prydin/classab-amp-mosfet/spice/class_ab.asc

C1: cap; 33µ
C2: cap; 68p
C3: cap; 100n
C4: cap; 220µ
C5: cap; 220p
C6: cap; 47µ
C7: cap; 159.2n
C8: cap; 79.62n
C9: cap; 79.62n
C10: cap; 7m
C12: cap; 7m
C105: cap; 240µ
C111: cap; 12µ
D2: diode; 1N4148
D4: zener; UMZ5_1N
D5: zener; UMZ5_1N
D7: diode; RFUH5TF6S
D8: diode; RFUH5TF6S
D9: diode; 1N4148
L1: ind; 10µ
L3: ind; 1m
L102: ind; 0.43m
L103: ind; 127m
M1: nmos; IRFP240
M2: pmos; IRFP9240
Q1: npn; 2N5550
Q2: npn; 2N5550
Q3: pnp; 2N5401
Q4: pnp; 2N5401
Q6: pnp; BD140C
Q7: npn; BD139C
Q8: npn; BD139C
Q11: npn; 2N5550
Q12: npn; 2N5550
Q15: npn; 2N5550
Q16: pnp; 2N5401
R1: res; 150
R2: res; 22k
R3: res; 470
R4: res; 470
R5: res; 470
R6: res; 4.7k
R7: res; 1k
R8: res; 330
R9: res; 22k
R10: res; 100
R11: res; 4.7k
R12: res; 410
R13: res; 10k
R14: res; 100
R15: res; 100
R16: res; 0.33
R17: res; 0.33
R18: res; 2k
R19: res; 1k
R20: res; 10
R21: res; 10
R22: res; 100
R23: res; 2k
R28: res; 1k
R31: res; 8
R32: res; 330
R114: res; 6
R122: res; 137
V1: voltage; 40
V2: voltage; PULSE(-1.2 1.2 0.5m 1n 1n 0.5m 1m); AC 0
V3: voltage; 40
V4: voltage; ""; AC 1
V5: voltage; SINE(0 0.3 1k)
Named nets: 0, IN, B-, B+, OUT, NEG_IN, FB
.tran 0 200m 0 500n
.four 1k 50 -1 v(out)
.option plotwinsize 0
.ac dec 1000 1 10000k
SPEAKER MODEL
-4.5V
0V
.param Freq=1k
.options plotwinsize=0 numdgt=15 NoOpiter
Simulation Parameters
.option NoMarch
.tran 0 {stop} {start} {maxstep}
.param numsamples=32
.options gminsteps=0 srcsteps=500
.param period {1/f1}
.param stop {start+sampletime}
It's often (meaning almost always) desirable to delay capturing samples for the FFT to let 
the DC conditions in the circuit stabilize.  Larger capacitors in the circuit require higher 
values of delay.  But, they charge up based on time, not cycles of the test frequency.
So, this delay is in *seconds.*
.param SettleTime=300m
.param start {delaycycles*period}
.param fftpts {2**fftlen}
.param maxstep {period/fftpts}
.param delaycycles {ceil(delay/period)}
Simulation Parameters - These are what you set for your simulation.
.param f1 {abs(Freq)}
.param delay {abs(SettleTime)}
.param fixedvin {abs(Vinput)*pkrms}
.param pkrms {sqrt(2)}
.param Vinput=1
RMS value of generator voltage.
.param fftlen {16}
.param sampletime {numsamples*period}
.four {Freq} V(out)
